maehw/DiyIrTower/doc/media/programmed-rcx.jpg

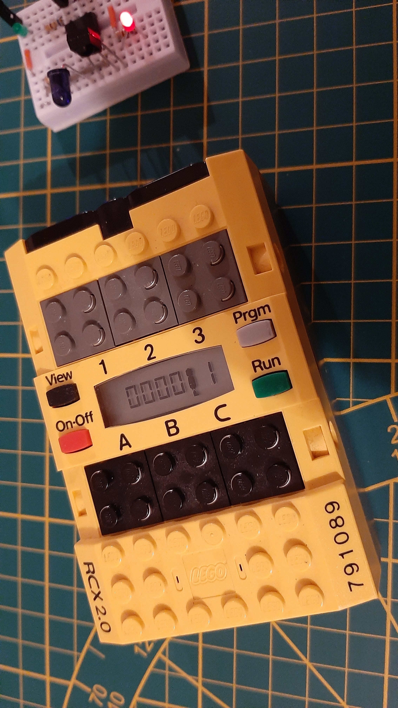
doc/media/programmed-rcx.jpg
